nhjschulz/EInkPicFrame/imgconverter/doc/select_gpl_file.png

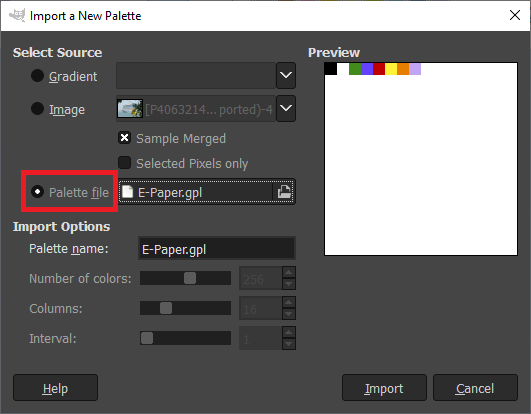
imgconverter/doc/select_gpl_file.png
