nhjschulz/EInkPicFrame/design/images/testimg.png

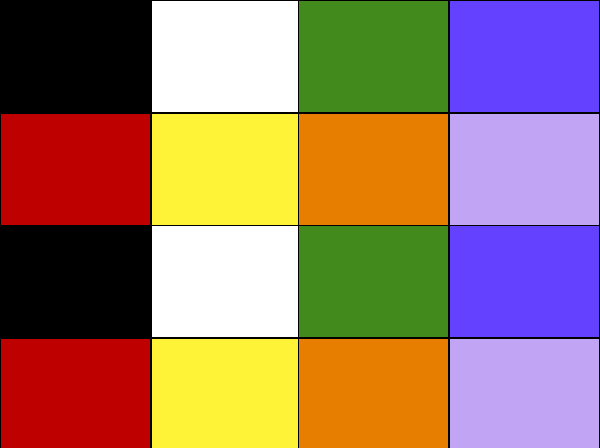
design/images/testimg.png
