nhjschulz/EInkPicFrame/include/Queue.h

/*
 * BSD 3-Clause License
 *
 * Copyright (c) 2021, Norbert Schulz
 * All rights reserved.
 *
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
 * 3. Neither the name of the copyright holder nor the names of its
 *    contributors may be used to endorse or promote products derived from
 *    this software without specific prior written permission.
 *
 * THIS SOFTWARE IS PROVIDED BY THE COPYRIGHT HOLDERS AND CONTRIBUTORS "AS IS"
 * AND ANY EXPRESS OR IMPLIED WARRANTIES, INCLUDING, BUT NOT LIMITED TO, THE
 * IMPLIED WARRANTIES OF MERCHANTABILITY AND FITNESS FOR A PARTICULAR PURPOSE ARE
 * DISCLAIMED. IN NO EVENT SHALL THE COPYRIGHT HOLDER OR CONTRIBUTORS BE LIABLE
 * FOR ANY DIRECT, INDIRECT, INCIDENTAL, SPECIAL, EXEMPLARY, OR CONSEQUENTIAL
 * DAMAGES (INCLUDING, BUT NOT LIMITED TO, PROCUREMENT OF SUBSTITUTE GOODS OR
 * SERVICES; LOSS OF USE, DATA, OR PROFITS; OR BUSINESS INTERRUPTION) HOWEVER
 * CAUSED AND ON ANY THEORY OF LIABILITY, WHETHER IN CONTRACT, STRICT LIABILITY,
 * OR TORT (INCLUDING NEGLIGENCE OR OTHERWISE) ARISING IN ANY WAY OUT OF THE USE
 * OF THIS SOFTWARE, EVEN IF ADVISED OF THE POSSIBILITY OF SUCH DAMAGE.
 */


#ifndef QUEUE_H_INCLUDED
#define QUEUE_H_INCLUDED

#include <stdint.h>

/** Implementation of a fixed size queue elements of type "T".
 *  The queue buffer is provided as a T array of N > 2 elements.
 *  The Queue capacity is one less the array entries. This space
 *  loss is due to emtpy vs. full detection.
 */
template<typename T>
class Queue
{
    public:

        /** Construct a queue with given buffer
         *  @param[in] buffer array with 'entries of T elements
         *  @param[in] number of entries in buffer
         */
        Queue(T buffer[], uint8_t entries);

        ~Queue()
        {
        }

        /** check if queue is empty */
        bool    isEmpty() const;

        /** check if queue is full */
        bool    isFull() const;

        /** get number of free slots */
        uint8_t available() const;

        /** get number of used slots */
        uint8_t used() const;

        /** reset the queue to be empty */
        void    clear();

        /** Add element to queue
         *  @param[in] element  element to copy into queue
         *  @return true of succesfull, false if queue full
         */
        bool    put(const T& element);

        /** Get element from queue
         * @param[out] element  destination for extracted element
         * @return true if element returned, false if queue empty
        */
        bool    get(T& element);

    private:

        uint8_t   m_wrIdx;           /**< next write position       */
        uint8_t   m_rdIdx;           /**< next read position        */
        uint8_t   m_size;            /**< allocated buffer space    */
        T*        m_buffer;          /**< memory for Queue elements */
};

// ---------------------- Iniliners ------------------------------------------

template <class T>
Queue<T>::Queue(T buffer[], uint8_t size) :
    m_wrIdx(0u),
    m_rdIdx(0u),
    m_size(size),
    m_buffer(buffer)
{
}

template <class T>
inline uint8_t Queue<T>::used() const
{
    uint8_t usedSlots(m_wrIdx);

    if (m_wrIdx >= m_rdIdx)
    {
        usedSlots -= m_rdIdx;
    }
    else
    {
        usedSlots  += m_size - m_rdIdx + 1;
    }

    return usedSlots;
}

template <class T>
inline uint8_t Queue<T>::available() const
{
    return m_size - this->used() - 1;
}

template <class T>
inline bool Queue<T>::isEmpty() const
{
    return m_wrIdx == m_rdIdx;
}

template <class T>
inline bool Queue<T>::isFull() const
{
    return this->used() == (m_size - 1);
}

template <class T>
inline void Queue<T>::clear()
{
    m_wrIdx = 0u;
    m_rdIdx = 0u;
}

template <class T>
inline bool Queue<T>::put(const T& element)
{
    uint8_t next((m_wrIdx + 1) % m_size); /**< next insert idx */
    bool    result(false);

    if (next != m_rdIdx)
    {
        // queue is not yet full

        m_buffer[next] = element;
        m_wrIdx = next;   /* atomic 8bit, no need for lock */
        result = true;
    }

    return result;
}

template <class T>
inline bool Queue<T>::get(T& element)
{
    bool result(false);

    if (!isEmpty())
    {
        uint8_t next((m_rdIdx + 1) % m_size); /**< next read idx */

        element = m_buffer[next];
        m_rdIdx = next;            /* atomic 8bit, no need for lock */
        result  = true;
    }

    return result;
}

/** A byte queue typedef to avoid ugly template syntax
 */
typedef Queue<uint8_t> ByteQueue;

#endif // QUEUE_H_INCLUDED
